PeterMitrano/sous-vide/CAD/NodeMCU/ESP8266 v7.SLDASM

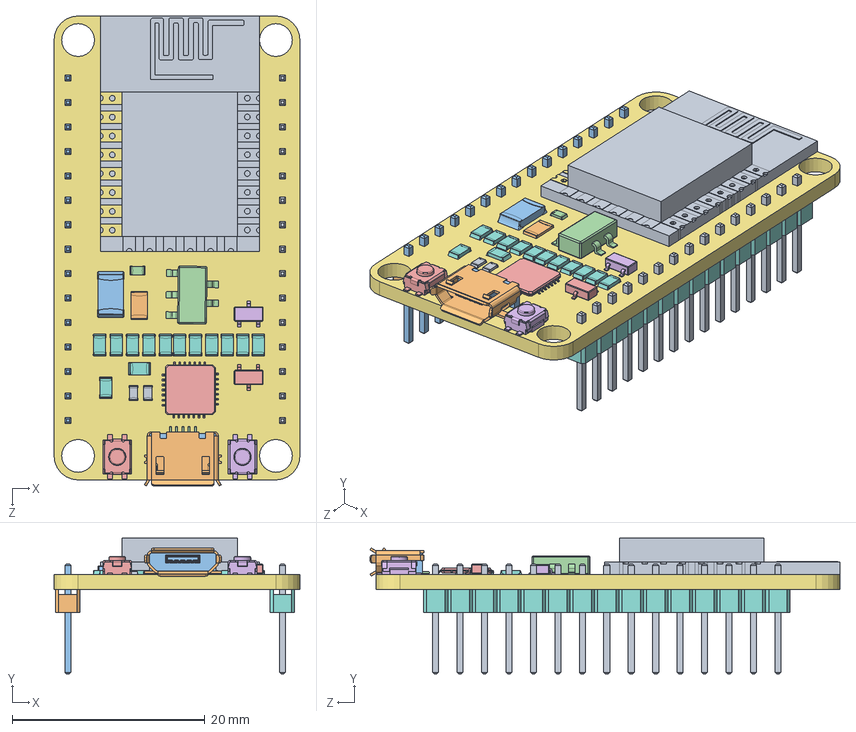
[picture p7: CAD file, 2017-12-30]
CAD/NodeMCU/ESP8266 v7.SLDASM
25.6 x 14.1 x 48.8 mm
ESP8266 v7
micro usb shell
micro usb internal
micro usb contact x 5
switch v1
switch v1 (1)
Placa Base
spacer x 15
pin x 15
spacer (1) (1) x 15
pin (1) (1) x 15
TSOP-5 v4 v1
TSOP-5 v4 v1 (1)
TSOP-5 v4 v1 (1) (1)
R0805-NO v1 x 13
R0805-NO v1 (1) x 2
R0805-NO v1 (1) (1)
R0805-NO v1 (1) (2)
R0805-NO v1 (1) (3)
Cuerpo Microprocesador v1
