PeterMitrano/sous-vide/CAD/16x2_LCD_Display/conductors.SLDPRT

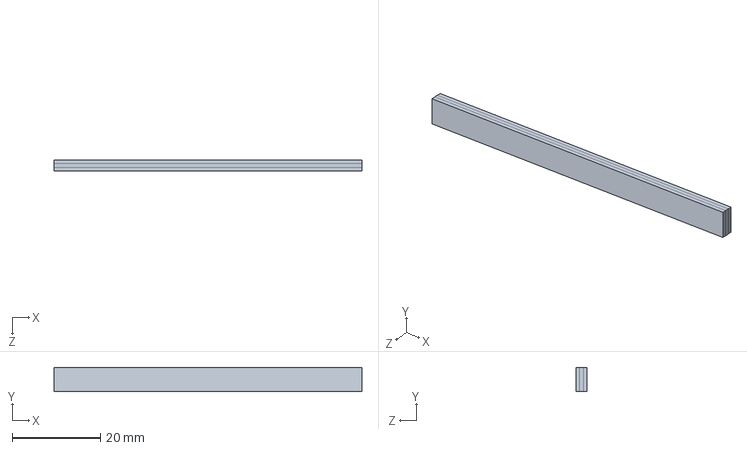
[picture p8: CAD file, 2017-12-30]
CAD/16x2_LCD_Display/conductors.SLDPRT
69.7 x 5.50 x 2.50 mm
