PeterMitrano/sous-vide/CAD/case_bottom.SLDPRT

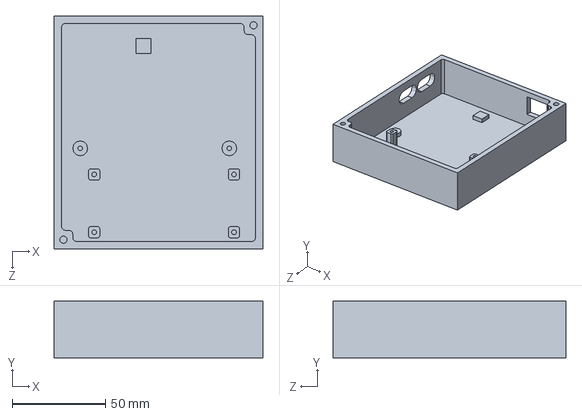
[picture p9: CAD file, 2018-01-30]
CAD/case_bottom.SLDPRT
112.0 x 30.5 x 125.0 mm
