PeterMitrano/sous-vide/CAD/components/T0-92_Molded_Narrow.stp

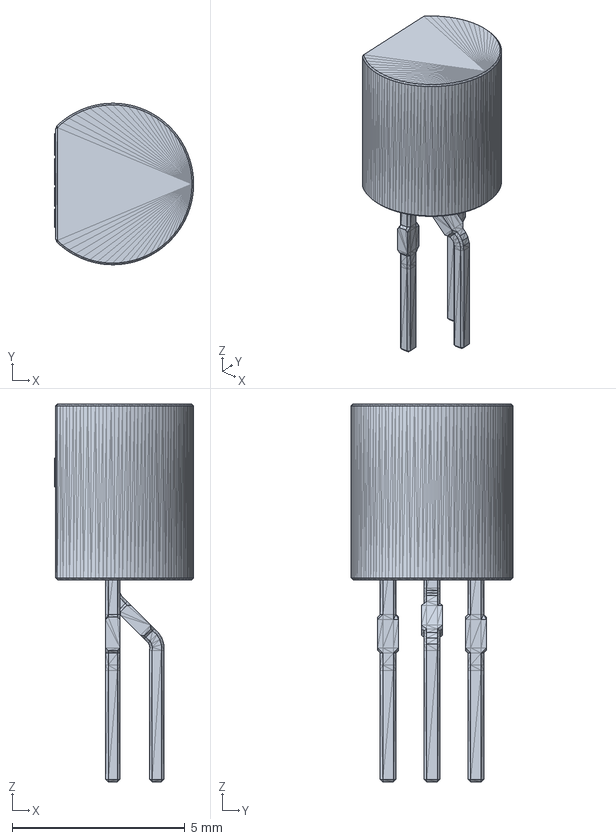
[picture p10: CAD file, 2018-01-09]
CAD/components/T0-92_Molded_Narrow.stp
4.03 x 4.67 x 10.9 mm
