PeterMitrano/sous-vide/CAD/components/Fuse_Holder_65600001009.fcstd

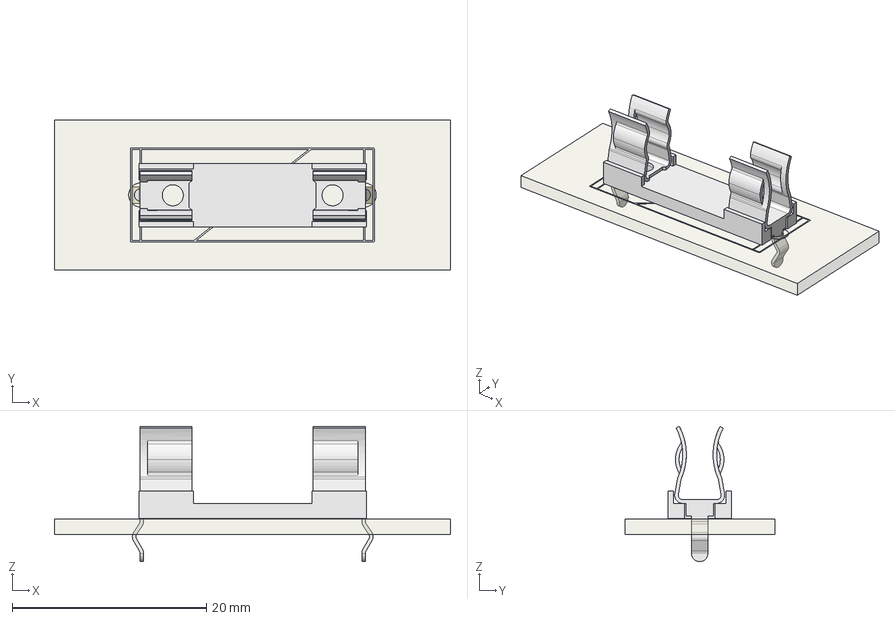
[picture p11: CAD file, 2018-01-09]
CAD/components/Fuse_Holder_65600001009.fcstd
40.8 x 15.4 x 13.9 mm
FrontSilk
TopPads
BotPads
PTHs
Pcb
Fuse_Holder_65600001009
