PeterMitrano/sous-vide/CAD/16x2_LCD_Display/LCD.SLDPRT

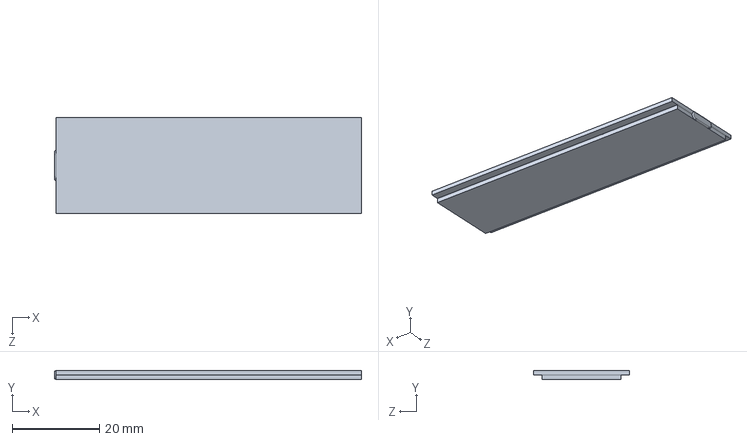
[picture p12: CAD file, 2017-12-30]
CAD/16x2_LCD_Display/LCD.SLDPRT
70.3 x 2.10 x 22.0 mm
