PeterMitrano/sous-vide/CAD/case_top.SLDPRT

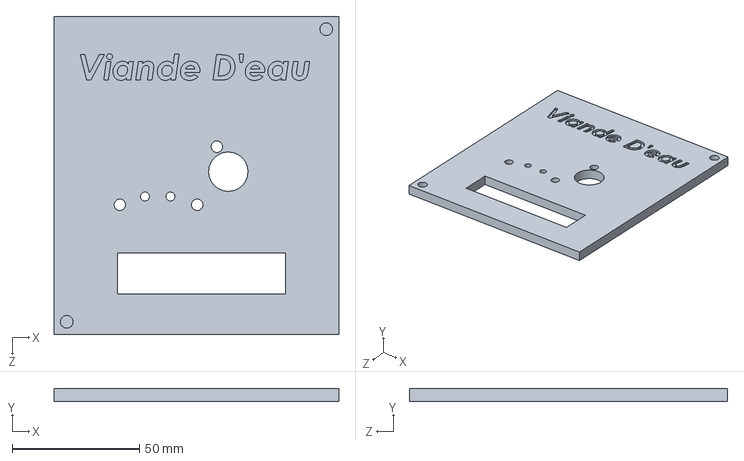
[picture p13: CAD file, 2018-01-30]
CAD/case_top.SLDPRT
112.0 x 5.08 x 125.0 mm
