PeterMitrano/sous-vide/CAD/components/P090S.stp

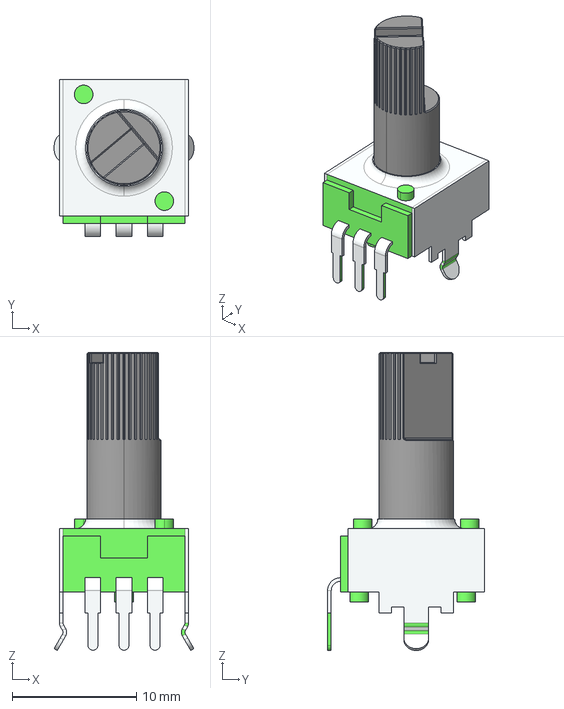
[picture p14: CAD file, 2018-01-09]
CAD/components/P090S.stp
11.3 x 12.7 x 24.0 mm
