PeterMitrano/sous-vide/CAD/16x2_LCD_Display/LCDbacklight.SLDPRT

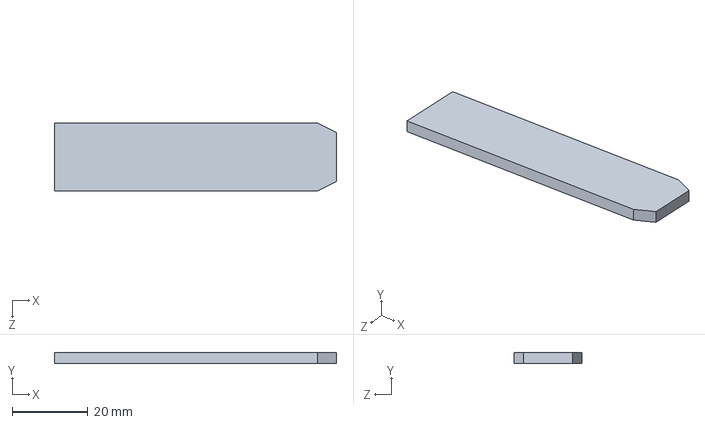
[picture p15: CAD file, 2017-12-30]
CAD/16x2_LCD_Display/LCDbacklight.SLDPRT
74.7 x 3.00 x 18.0 mm
