PeterMitrano/sous-vide/CAD/components/fx0321.stp

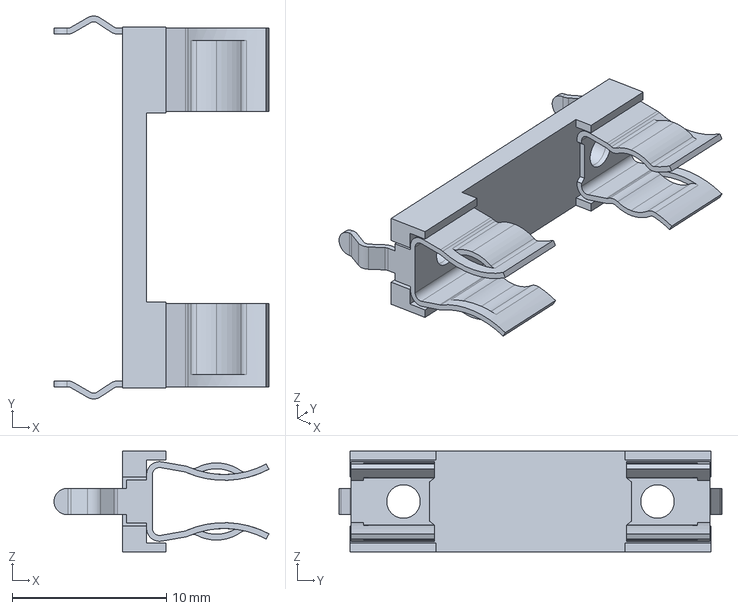
[picture p16: CAD file, 2018-01-09]
CAD/components/fx0321.stp
13.9 x 24.8 x 6.54 mm
