PeterMitrano/sous-vide/CAD/fancy_knob_for_cnc.SLDPRT

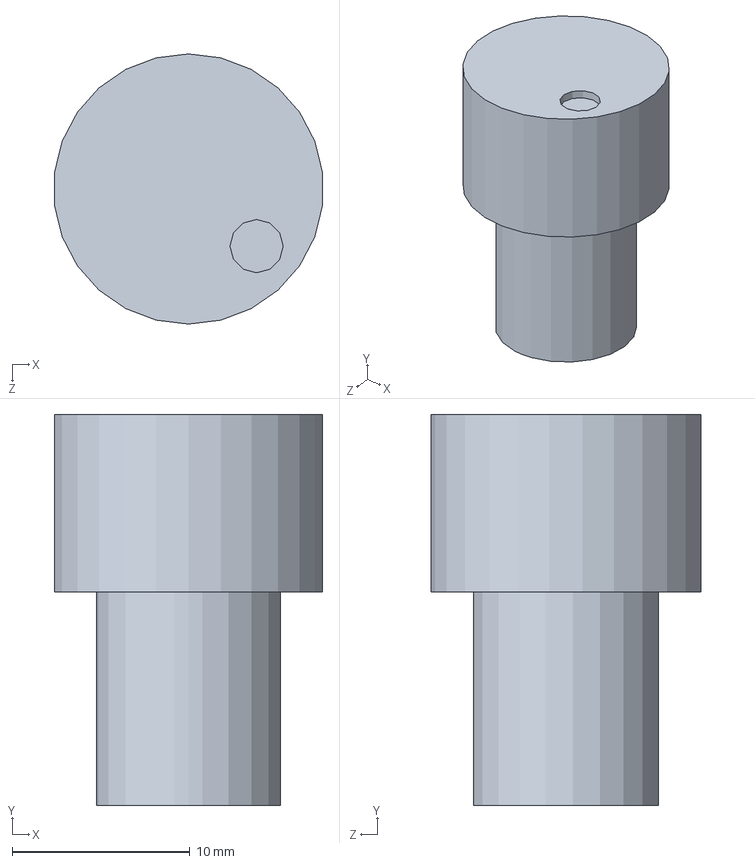
[picture p17: CAD file, 2018-01-30]
CAD/fancy_knob_for_cnc.SLDPRT
15.1 x 22.0 x 15.2 mm
