PeterMitrano/sous-vide/CAD/16x2_LCD_Display/LCD_PCB.SLDPRT

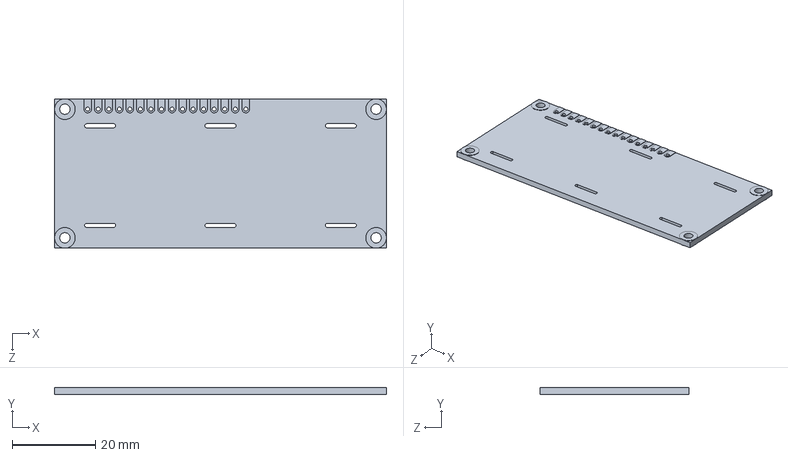
[picture p18: CAD file, 2017-12-30]
CAD/16x2_LCD_Display/LCD_PCB.SLDPRT
80.0 x 1.80 x 36.0 mm
