PeterMitrano/sous-vide/CAD/board/LED_D5.0mm_001.sldprt

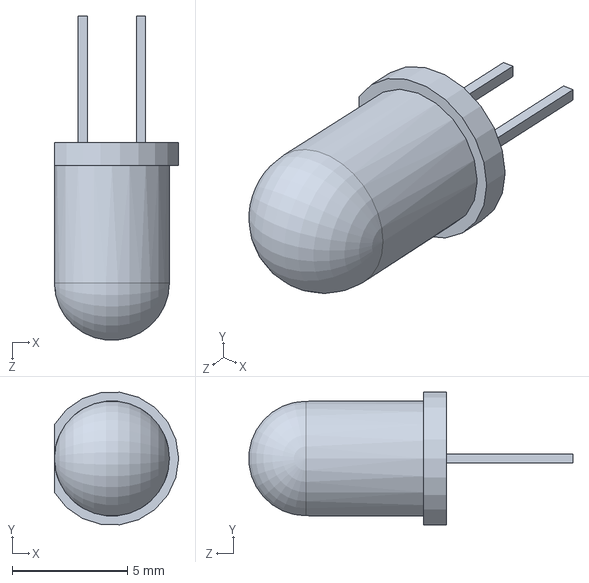
[picture p19: CAD file, 2018-01-09]
CAD/board/LED_D5.0mm_001.sldprt
5.40 x 5.76 x 14.1 mm
