PeterMitrano/sous-vide/CAD/button_holder.SLDPRT

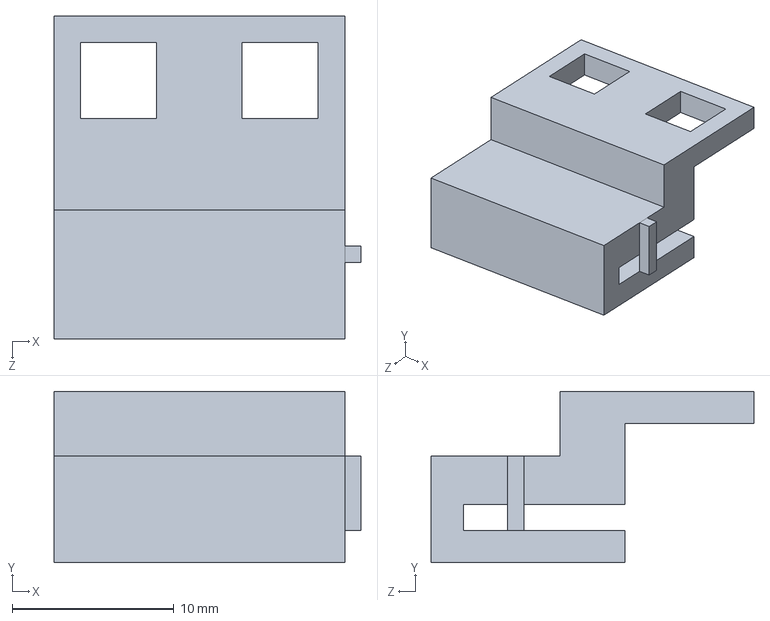
[picture p20: CAD file, 2018-01-29]
CAD/button_holder.SLDPRT
19.0 x 10.6 x 20.0 mm
