PeterMitrano/sous-vide/CAD/components/female_header_a-bl254-eg-z15d.stp

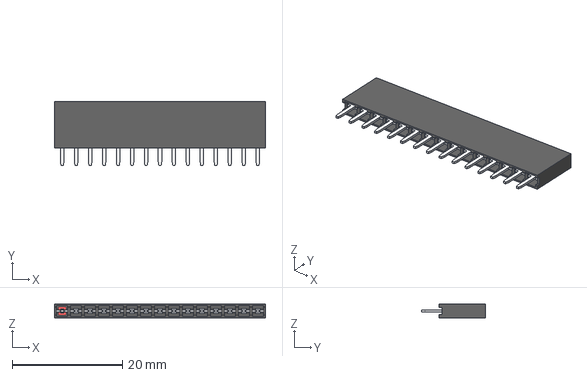
[picture p21: CAD file, 2018-01-09]
CAD/components/female_header_a-bl254-eg-z15d.stp
38.4 x 11.7 x 2.50 mm
