PeterMitrano/sous-vide/CAD/16x2_LCD_Display/metal_casing.SLDPRT

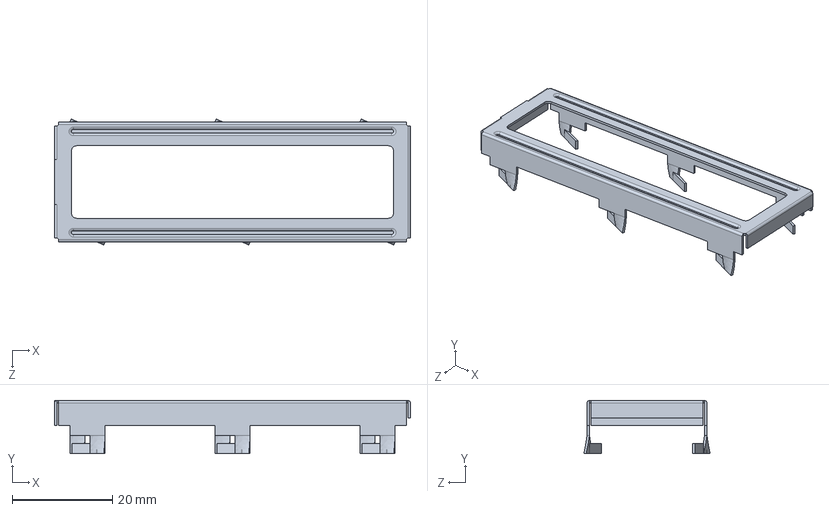
[picture p22: CAD file, 2017-12-30]
CAD/16x2_LCD_Display/metal_casing.SLDPRT
71.2 x 10.6 x 25.3 mm
