PeterMitrano/sous-vide/CAD/components/g5le-1-e_5dc.stp

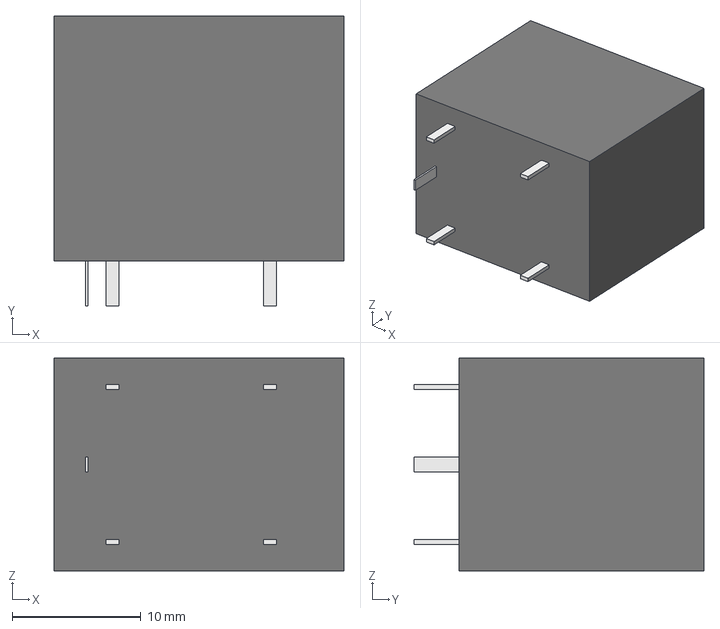
[picture p23: CAD file, 2018-01-09]
CAD/components/g5le-1-e_5dc.stp
22.5 x 22.5 x 16.5 mm
