PeterMitrano/sous-vide/CAD/fancy_knob_for_printing.SLDPRT

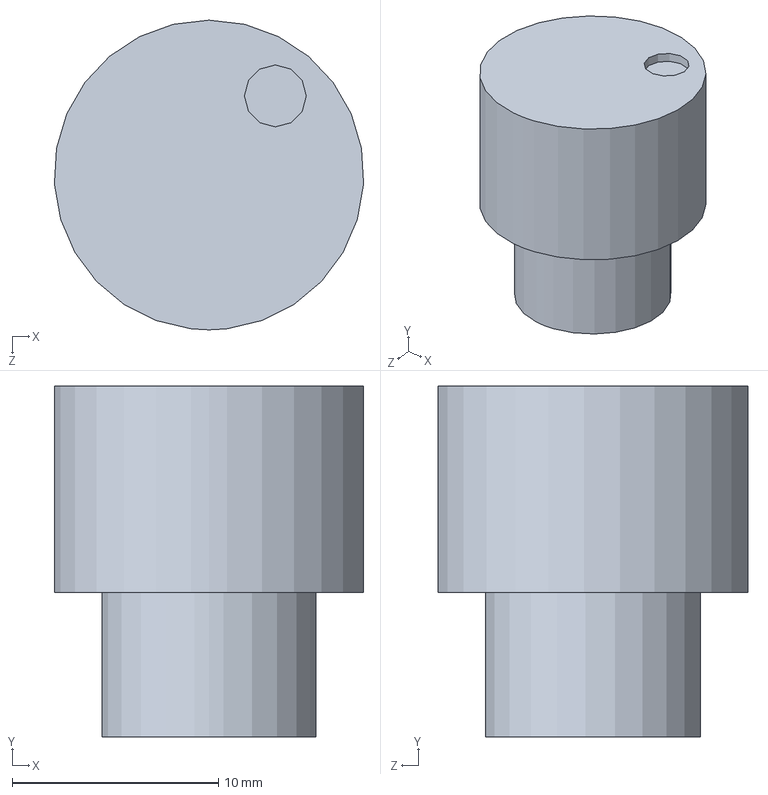
[picture p24: CAD file, 2018-01-25]
CAD/fancy_knob_for_printing.SLDPRT
15.0 x 17.0 x 15.0 mm
