PeterMitrano/sous-vide/CAD/components/nc6-p108-02.stp

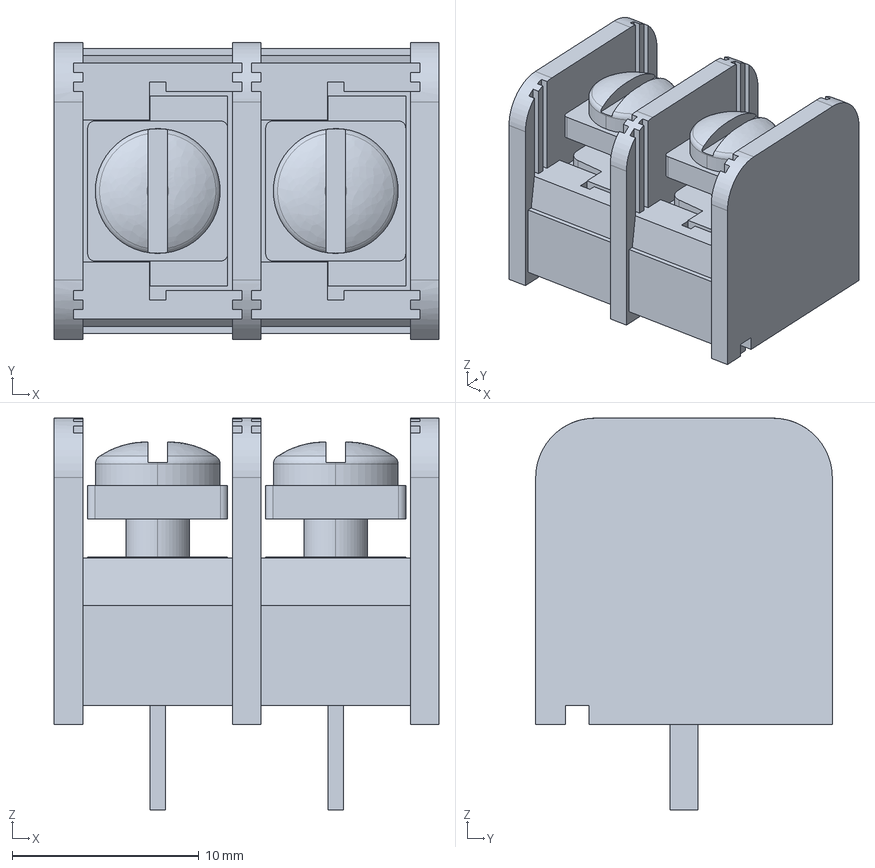
[picture p25: CAD file, 2018-01-09]
CAD/components/nc6-p108-02.stp
20.6 x 15.9 x 21.0 mm
