PeterMitrano/sous-vide/CAD/led_contact.SLDPRT

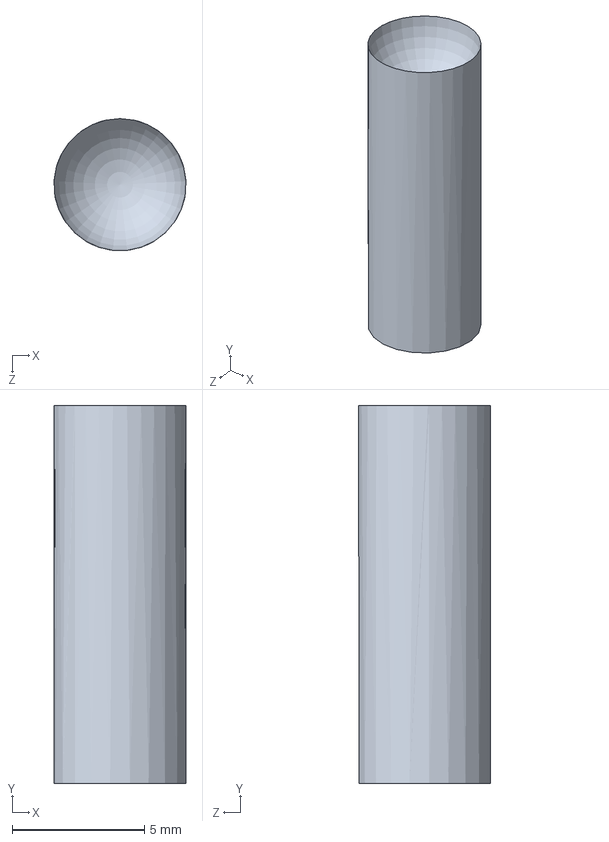
[picture p26: CAD file, 2018-01-12]
CAD/led_contact.SLDPRT
4.99 x 14.3 x 4.99 mm
