PeterMitrano/sous-vide/CAD/components/RAC01-05SC.fcstd

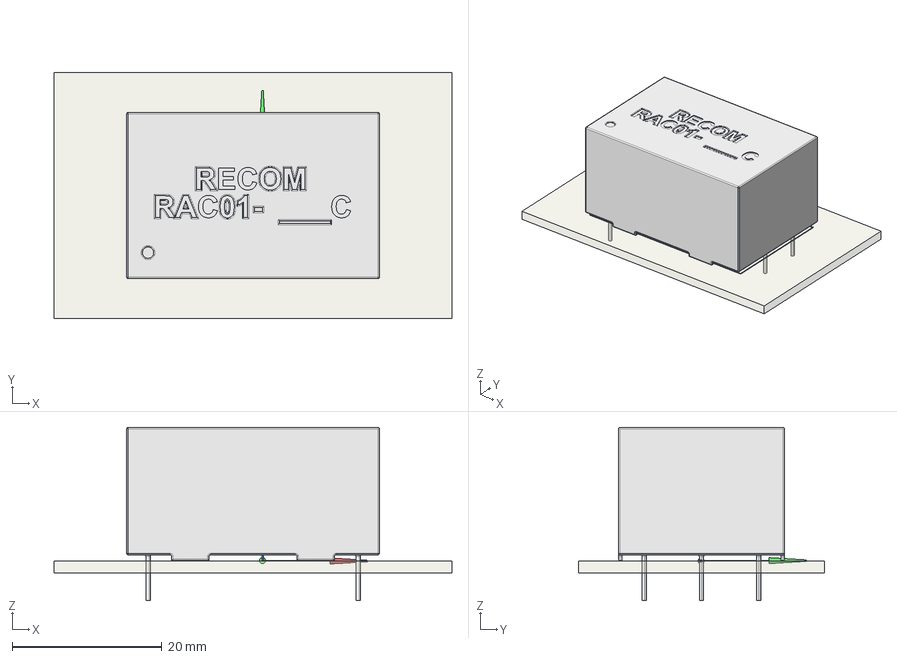
[picture p27: CAD file, 2018-01-09]
CAD/components/RAC01-05SC.fcstd
53.1 x 32.8 x 23.1 mm
FrontSilk
TopPads
BotPads
PTHs
Pcb
Z
Y
X
RAC01-05SC
