PeterMitrano/sous-vide/CAD/lcd_backpack.SLDPRT

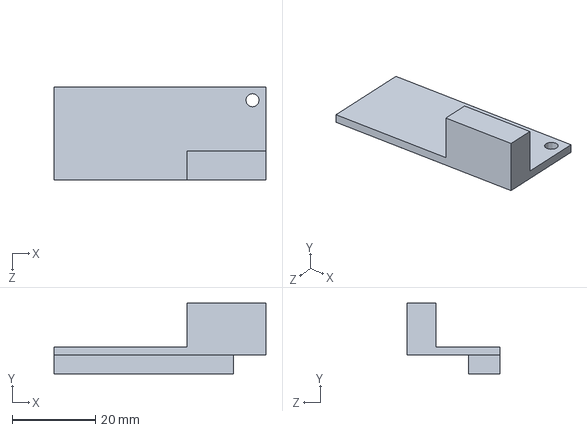
[picture p28: CAD file, 2018-01-11]
CAD/lcd_backpack.SLDPRT
51.0 x 17.0 x 22.4 mm
