PeterMitrano/sous-vide/CAD/button_contact.SLDPRT

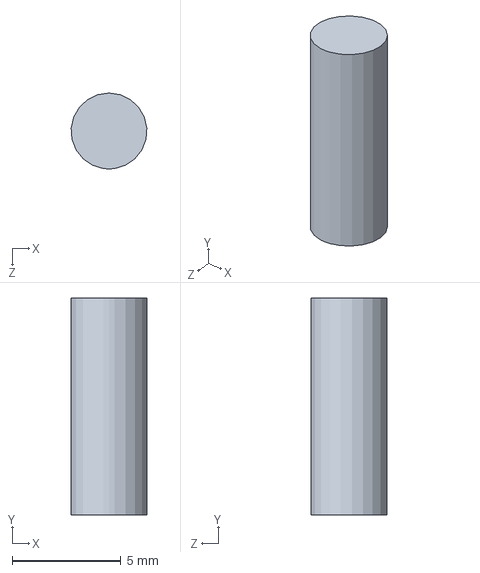
[picture p29: CAD file, 2018-01-09]
CAD/button_contact.SLDPRT
3.49 x 10.0 x 3.50 mm
