PeterMitrano/sous-vide/CAD/components/G5LE_1_E.fcstd

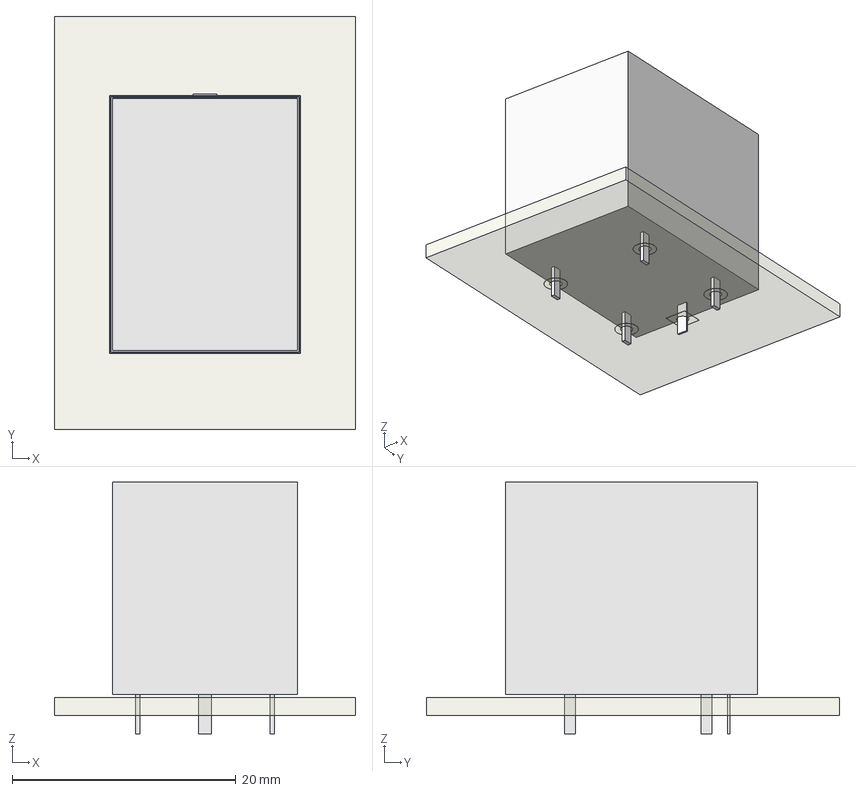
[picture p30: CAD file, 2018-01-09]
CAD/components/G5LE_1_E.fcstd
26.9 x 36.9 x 22.5 mm
F_CrtYd
FrontSilk
TopPads
BotPads
PTHs
Pcb
g5le-1-e_5dc
