PeterMitrano/sous-vide/CAD/components/B3F_1000.step

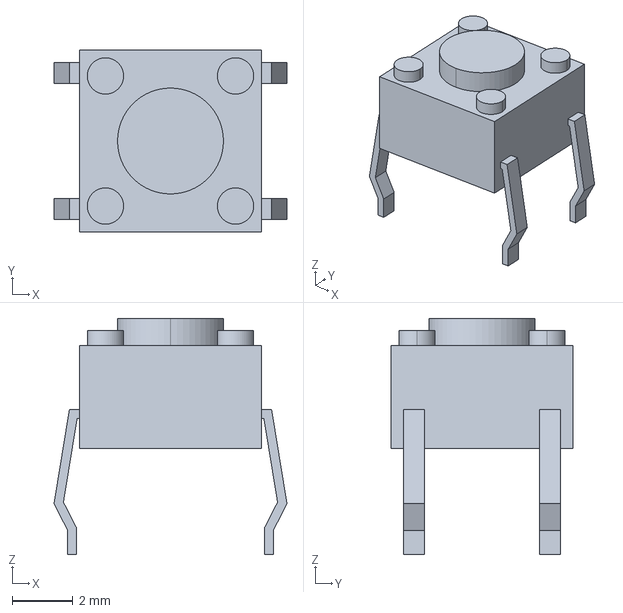
[picture p31: CAD file, 2018-01-09]
CAD/components/B3F_1000.step
7.70 x 6.00 x 7.80 mm
