PeterMitrano/sous-vide/CAD/NodeMCU/pin.sldprt

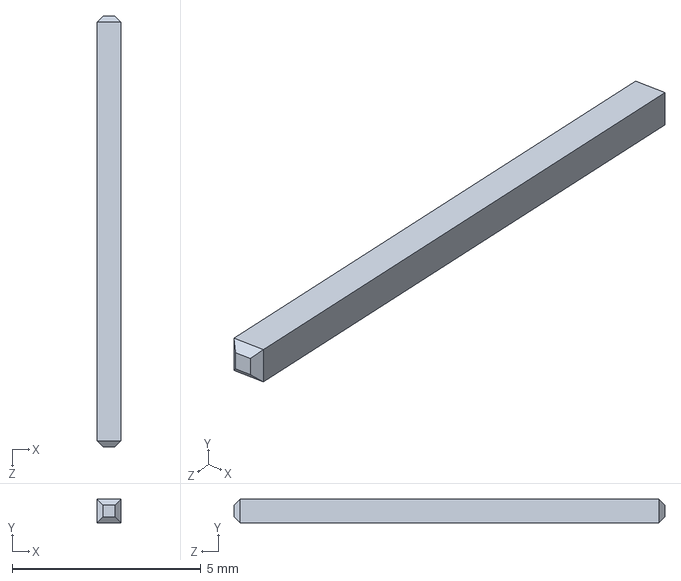
[picture p32: CAD file, 2017-12-30]
CAD/NodeMCU/pin.sldprt
0.635 x 0.635 x 11.4 mm
